felipeespitalher/printer/Delta/1454066755.png

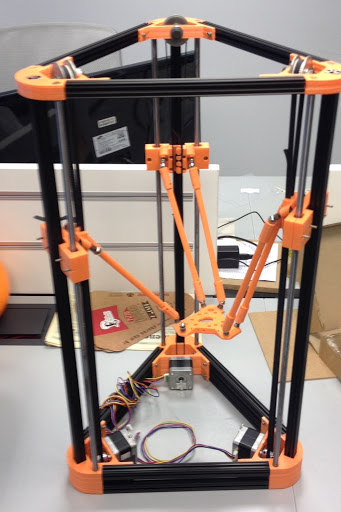
Delta/1454066755.png
