felipeespitalher/printer/Delta/20151126085155.jpg

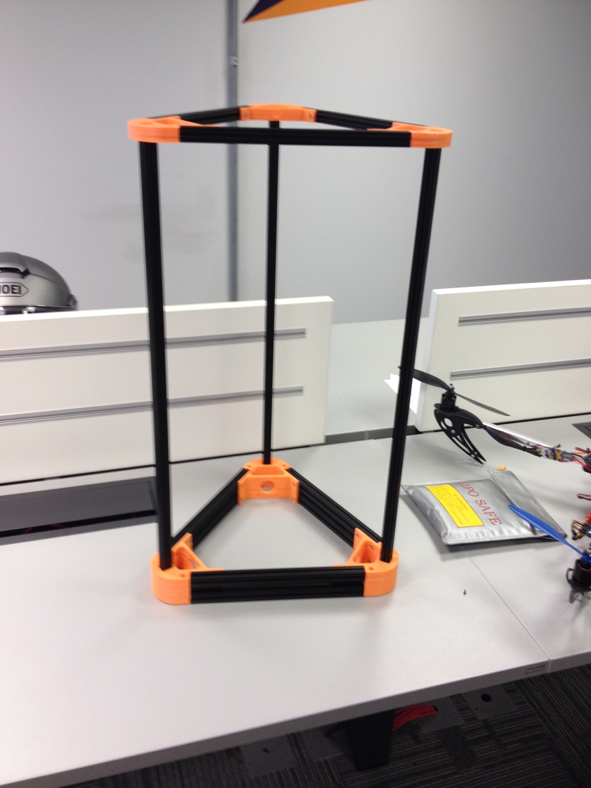
Delta/20151126085155.jpg
